rupret007/Rad-Dad-Merch/release/v9/previews/Rad_Dad_Cassette_v38_DETAIL.png

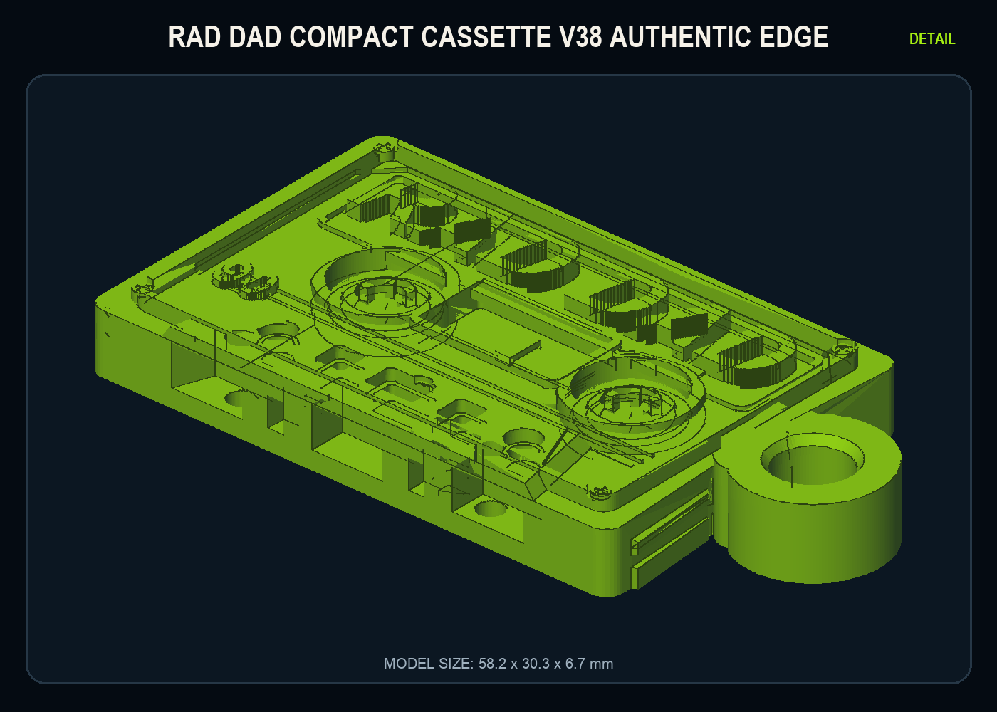
release/v9/previews/Rad_Dad_Cassette_v38_DETAIL.png
