rupret007/Rad-Dad-Merch/release/v9/previews/Rad_Dad_Cassette_v38_FRONT.png

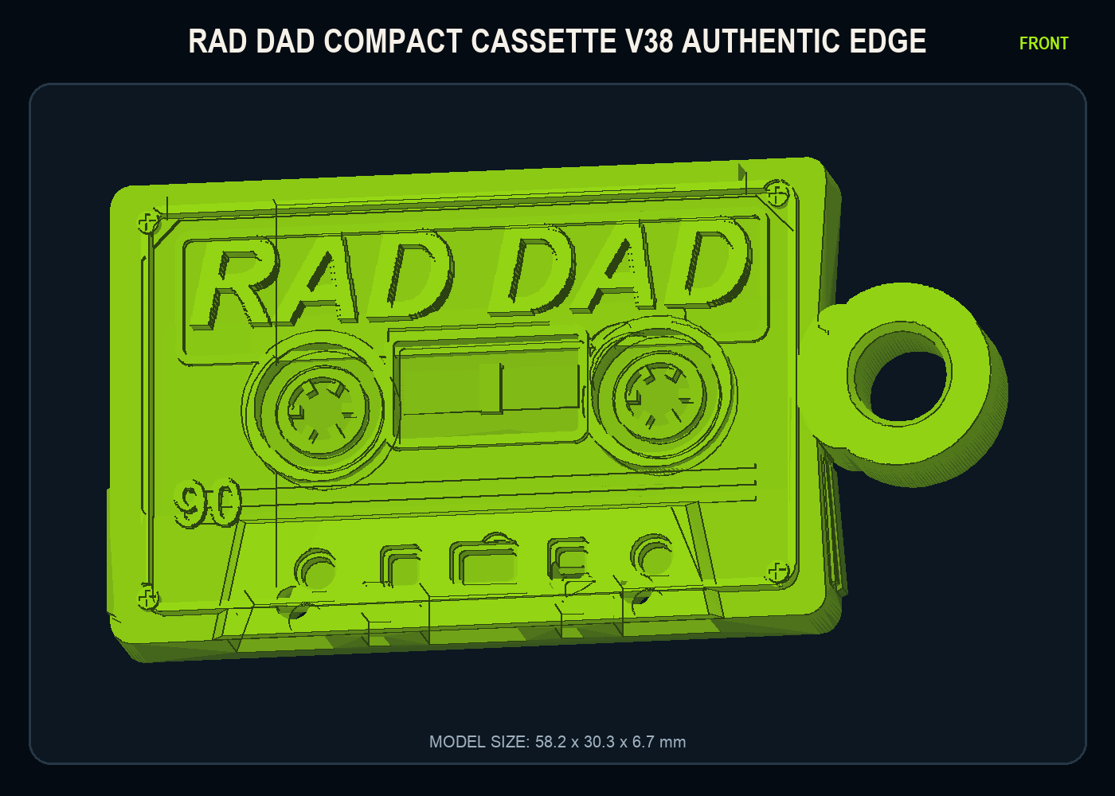
release/v9/previews/Rad_Dad_Cassette_v38_FRONT.png
