rupret007/Rad-Dad-Merch/release/v9/previews/Rad_Dad_Retro_Riot_v9_ALL_FOUR_DETAIL.png

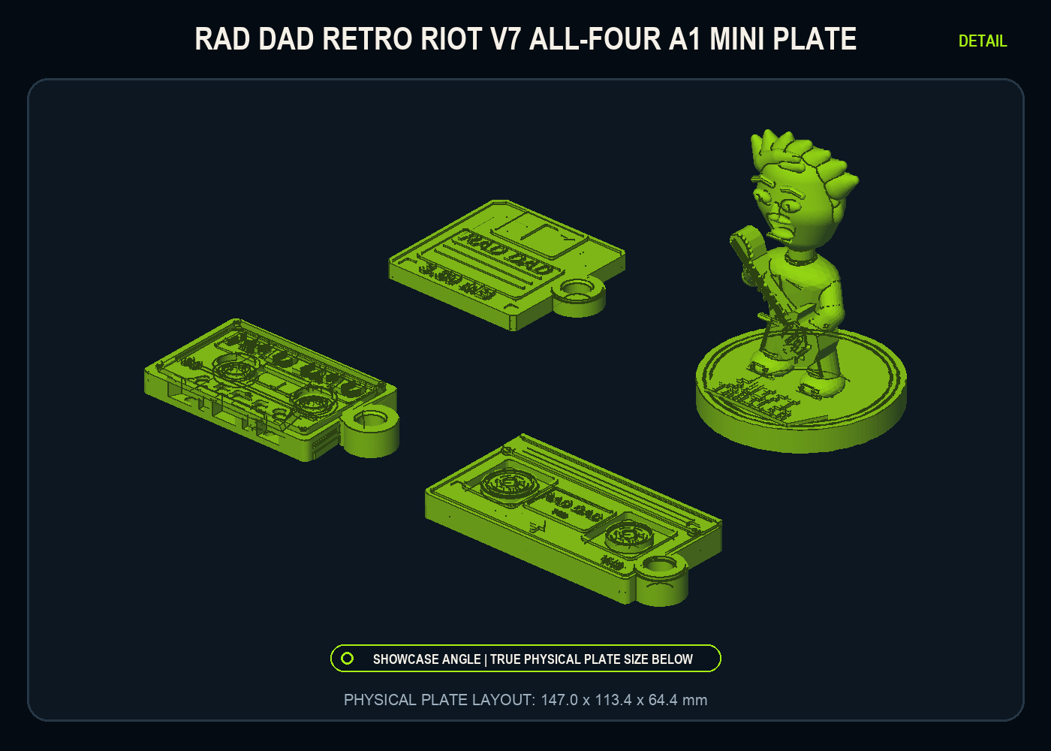
release/v9/previews/Rad_Dad_Retro_Riot_v9_ALL_FOUR_DETAIL.png
