rupret007/Rad-Dad-Merch/release/v9/previews/Trailer_Swift_v16_Strat_Style_Punk_QR_DETAIL.png

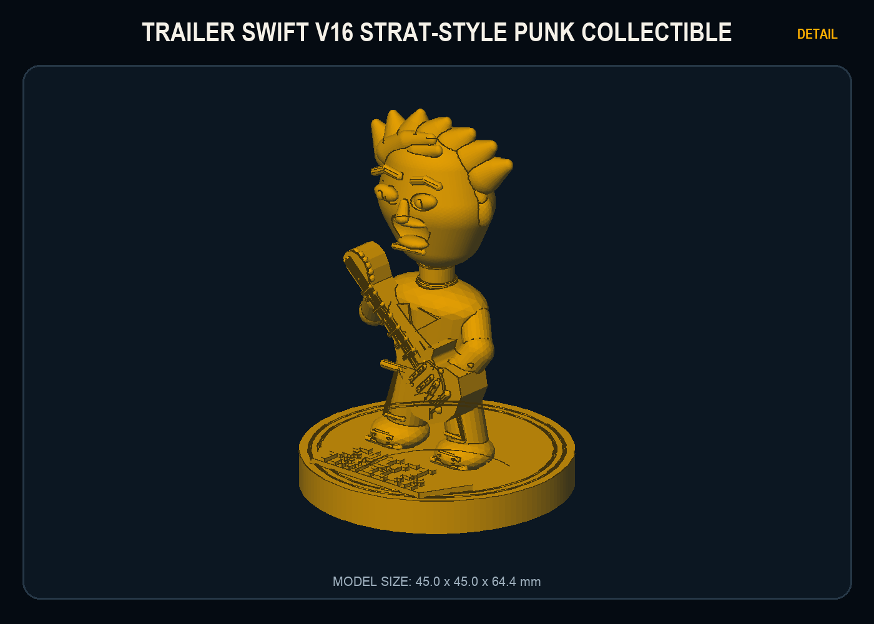
release/v9/previews/Trailer_Swift_v16_Strat_Style_Punk_QR_DETAIL.png
