rupret007/Rad-Dad-Merch/release/v7/guides/nfc_overlays/Rad_Dad_25MM_TRAILER_SWIFT_TAP_NFC_OVERLAY_LABEL.pdf

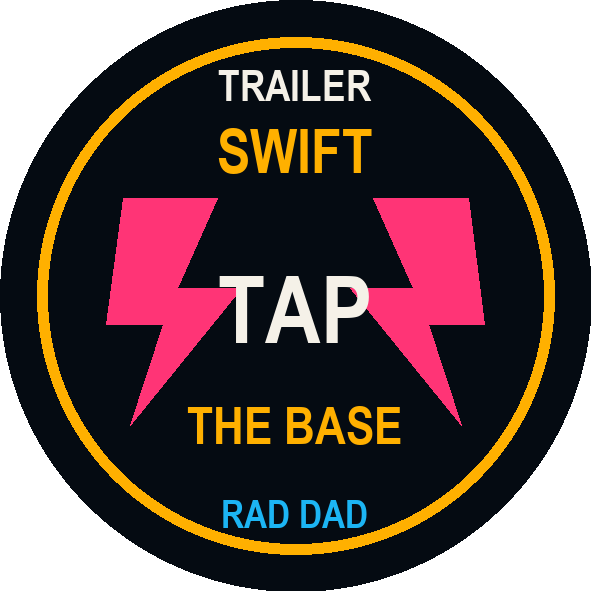
[picture p31: page 1]
