rupret007/Rad-Dad-Merch/release/v7/guides/nfc_overlays/Rad_Dad_25MM_VHS_TAP_NFC_OVERLAY_LABEL.pdf

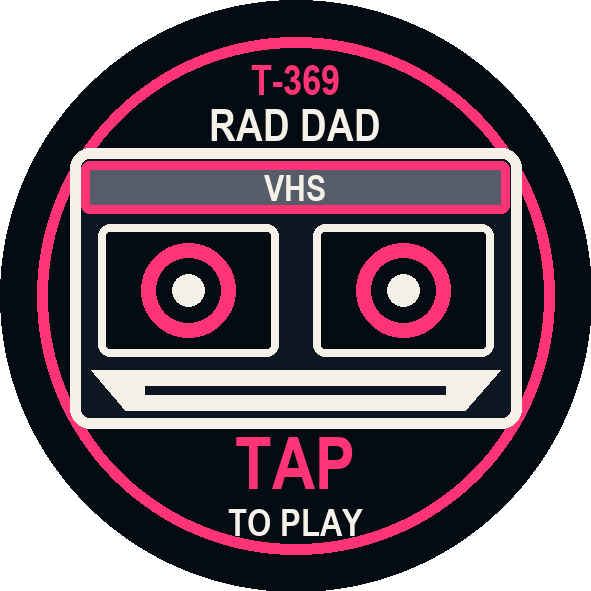
[picture p32: page 1]
