rupret007/Rad-Dad-Merch/release/v8/guides/qr_stickers/Rad_Dad_QR_STICKERS_AVERY_6450_OL1025_63UP_US_LETTER.pdf

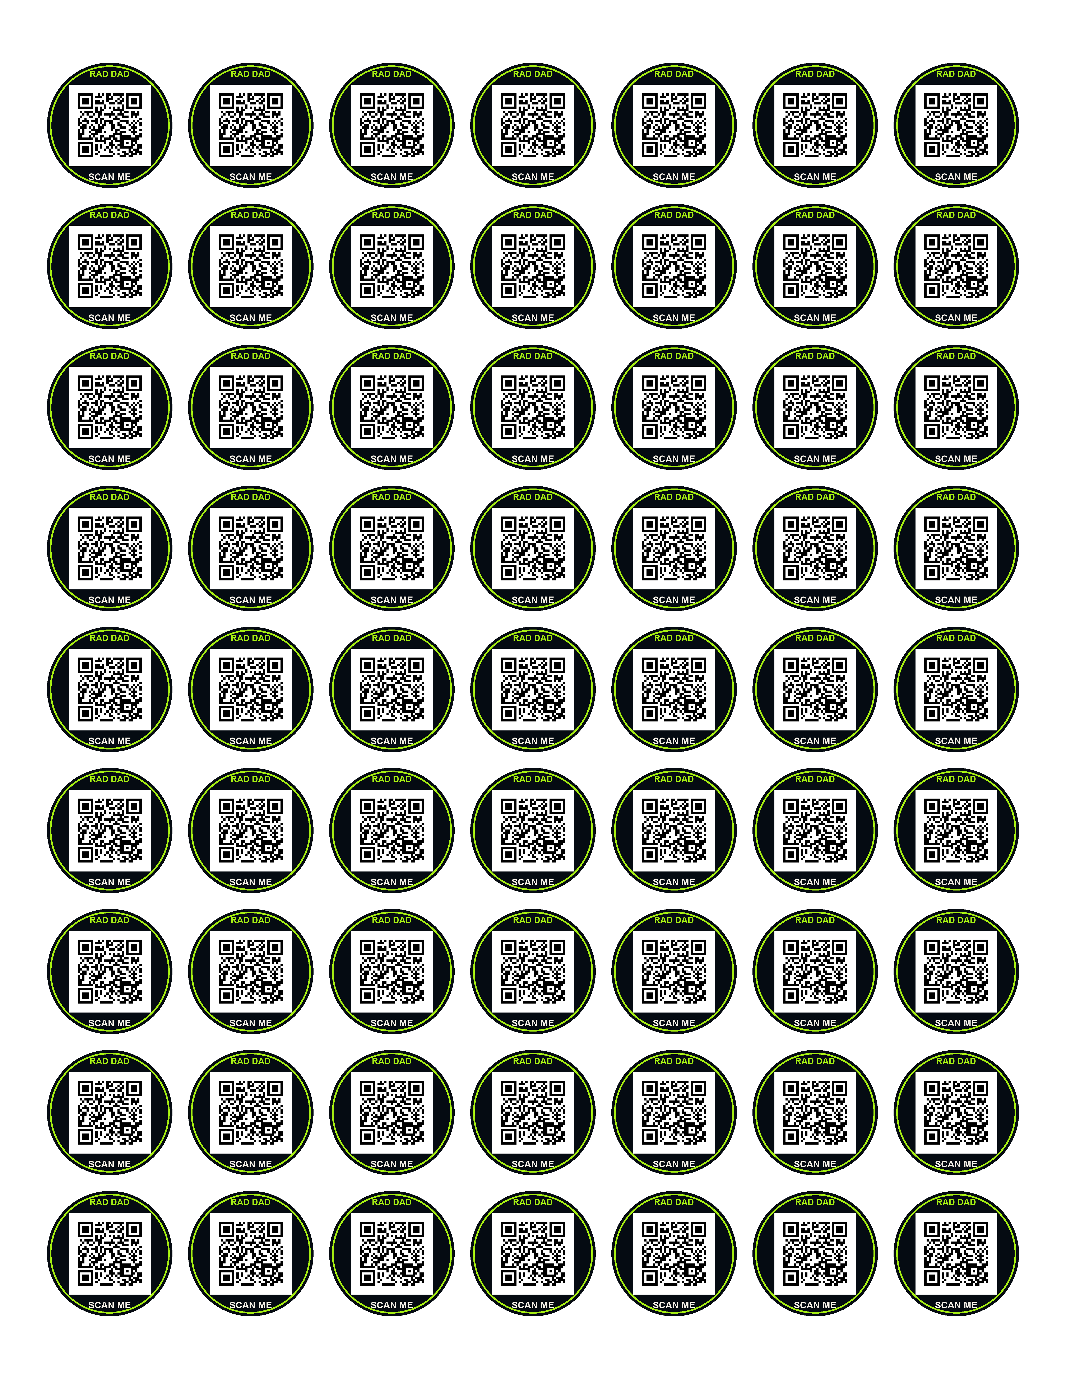
[picture p33: page 1]
