rupret007/Rad-Dad-Merch/release/v8/guides/qr_stickers/Rad_Dad_QR_STICKERS_HAND_CUT_35UP_US_LETTER.pdf

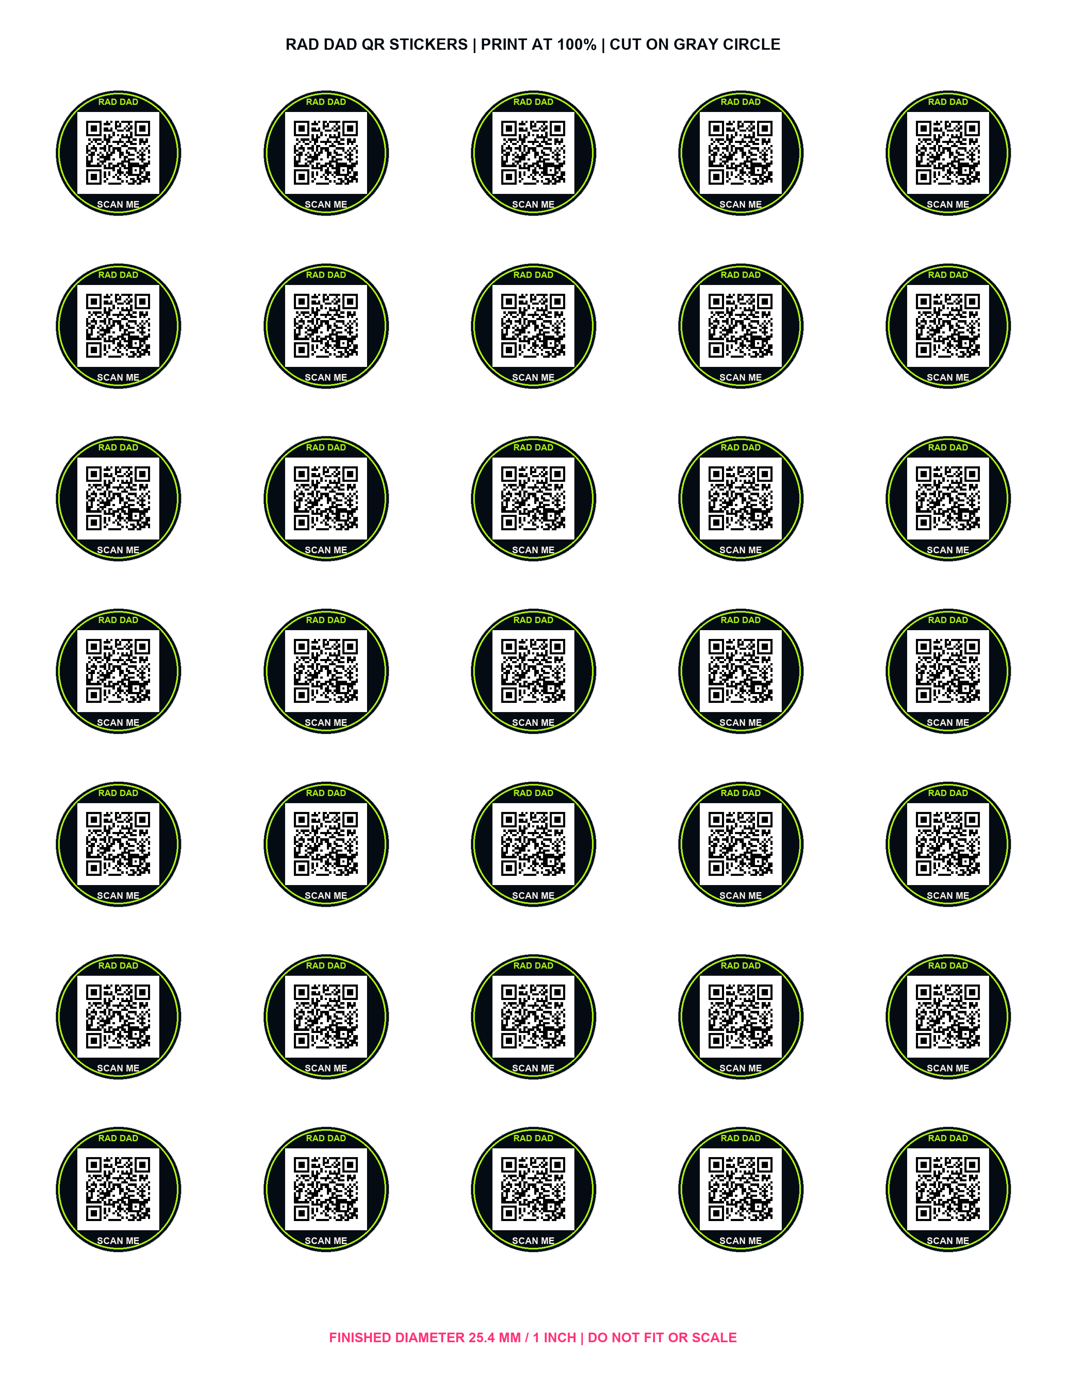
[picture p34: page 1]
