rupret007/Rad-Dad-Merch/release/v8/guides/qr_stickers/Rad_Dad_QR_STICKER_PRINT_CALIBRATION.pdf

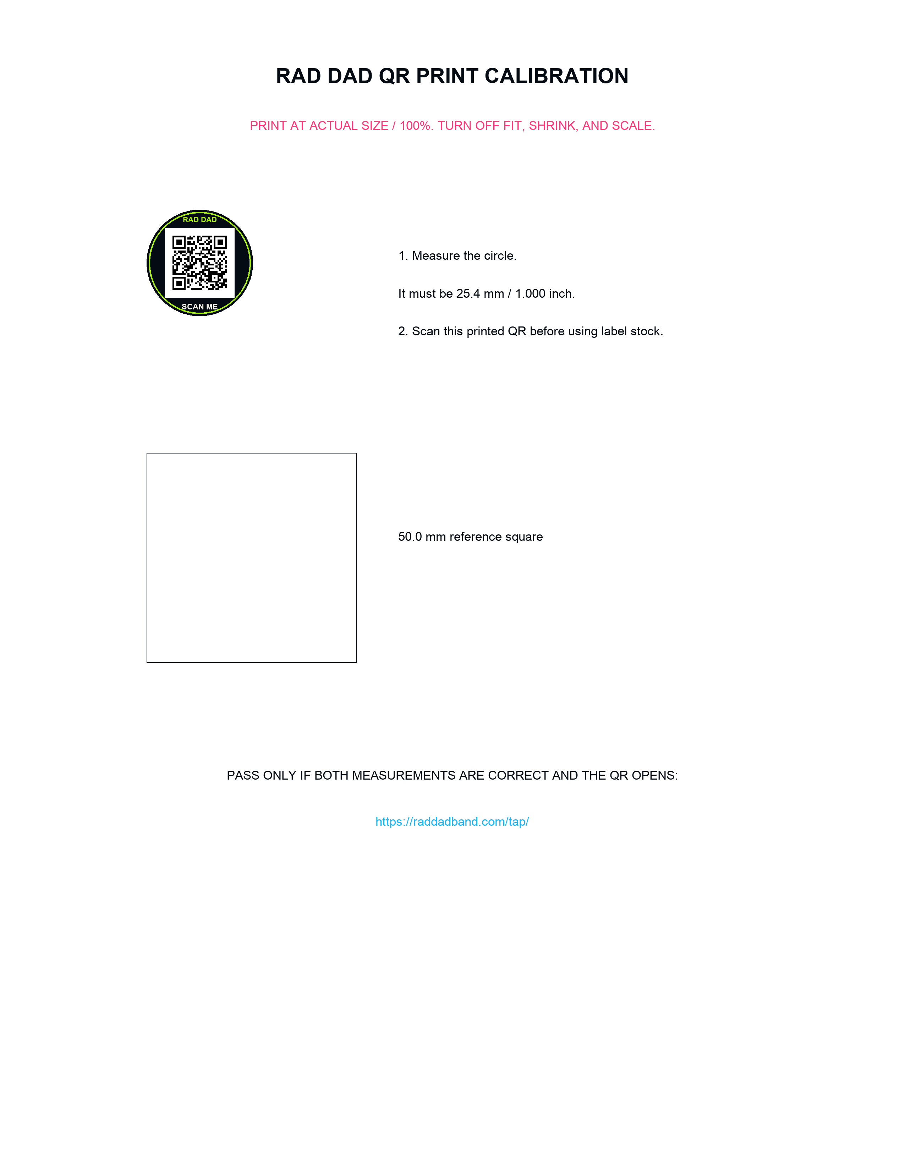
[picture p38: page 1]
